Zhiqing-Xu/Filter_Life_Measurement/Design Draft/figs/5.jpg

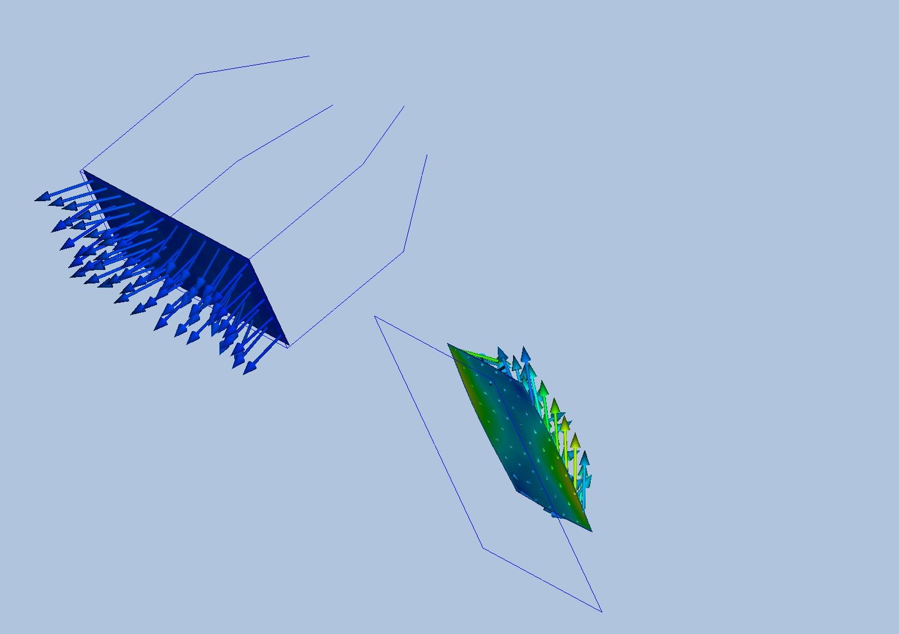
Design Draft/figs/5.jpg
