Zhiqing-Xu/Filter_Life_Measurement/Design Draft/Project01-APS490-CAD-CFD/CAD-Whole Sys Draft/blower/QUAT CAO AP.JPG

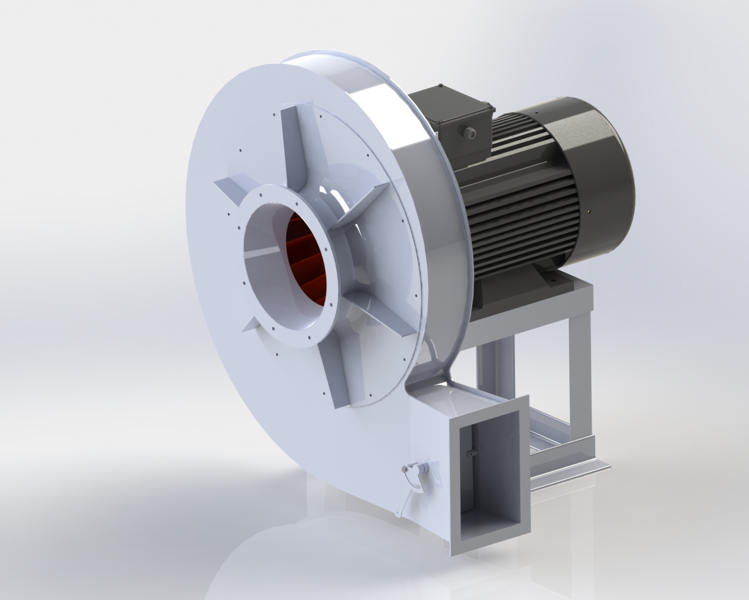
Design Draft/Project01-APS490-CAD-CFD/CAD-Whole Sys Draft/blower/QUAT CAO AP.JPG
