Zhiqing-Xu/Filter_Life_Measurement/Design Draft/Project01-APS490-CAD-CFD/CAD-Whole Sys Draft/butterfly valve/Sanitary-butterfly-valve-DIN11851-MxM-CAD-model-DN50-NO.jpg

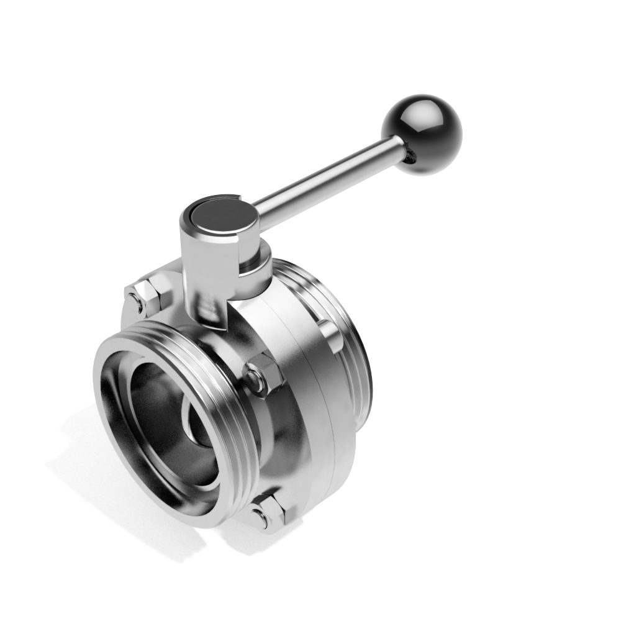
Design Draft/Project01-APS490-CAD-CFD/CAD-Whole Sys Draft/butterfly valve/Sanitary-butterfly-valve-DIN11851-MxM-CAD-model-DN50-NO.jpg
