Zhiqing-Xu/Filter_Life_Measurement/Design Draft/Project01-APS490-CAD-CFD/CAD-Whole Sys Final/other/Renderings/untitled.541.jpg

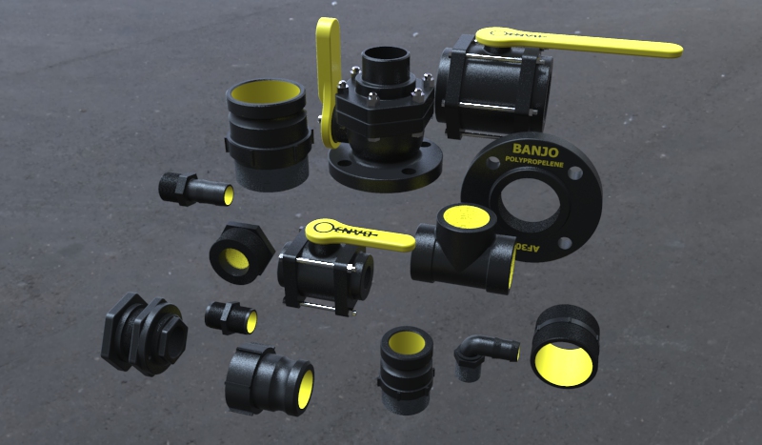
Design Draft/Project01-APS490-CAD-CFD/CAD-Whole Sys Final/other/Renderings/untitled.541.jpg
