Zhiqing-Xu/Filter_Life_Measurement/Design Draft/Project01-APS490-CAD-CFD/CFD/cfd_test_04/Design 1/Scenario 1/thumbnail.jpg

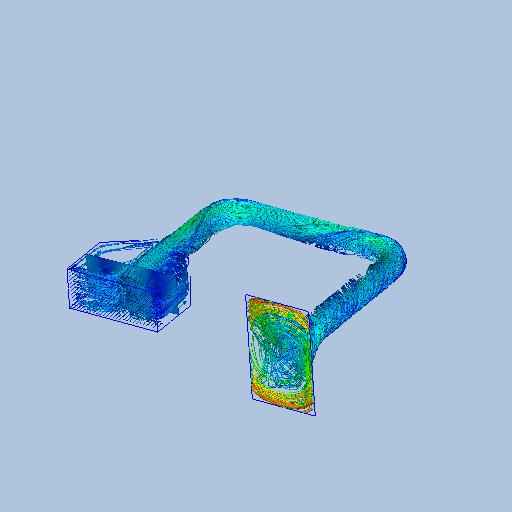
Design Draft/Project01-APS490-CAD-CFD/CFD/cfd_test_04/Design 1/Scenario 1/thumbnail.jpg
