Zhiqing-Xu/Filter_Life_Measurement/Final Design/FD_PNID.jpg

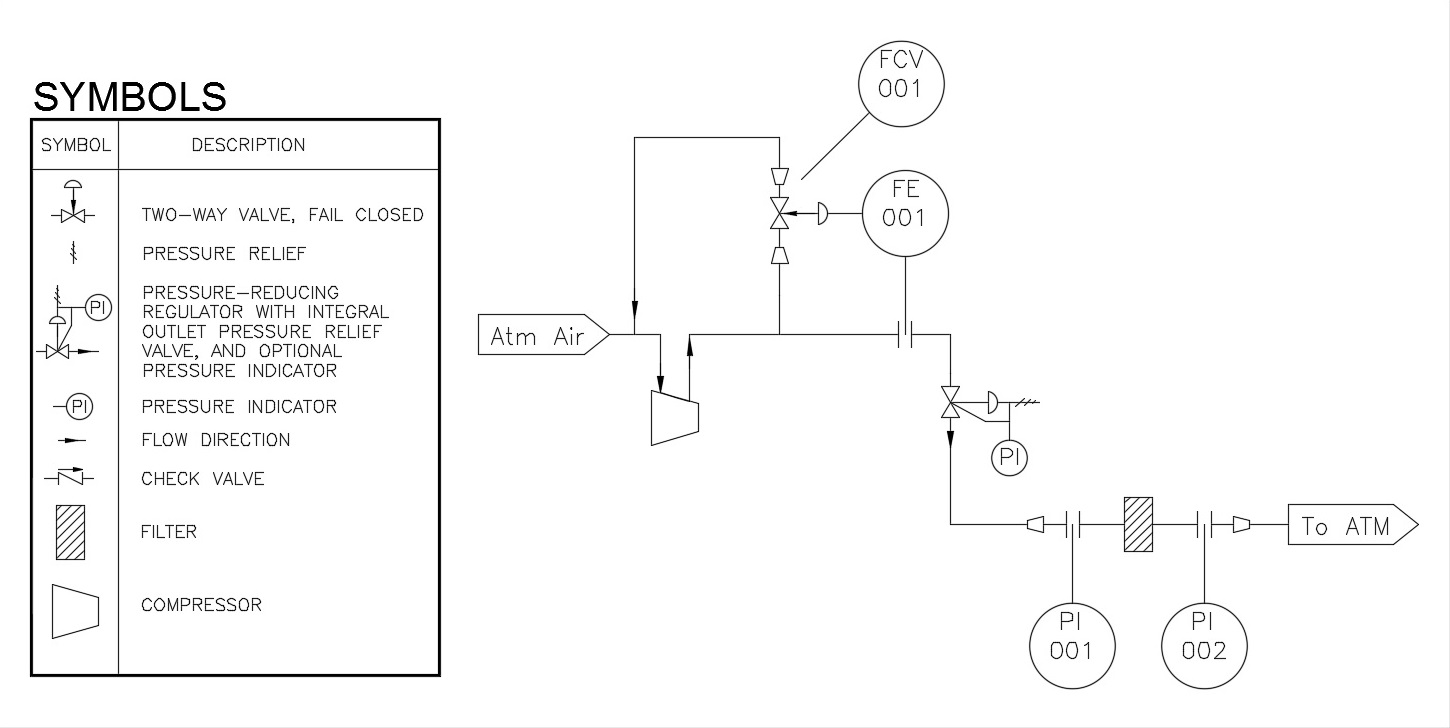
Final Design/FD_PNID.jpg
