Zhiqing-Xu/Filter_Life_Measurement/Final Design/Final Report Pik/1.png

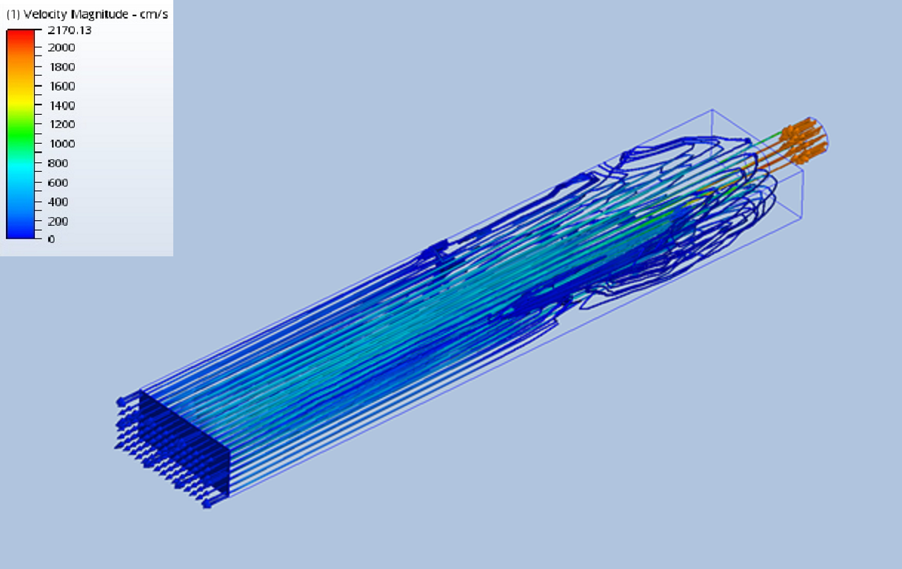
Final Design/Final Report Pik/1.png
