Zhiqing-Xu/Filter_Life_Measurement/Final Design/Project01-APS490-CAD-CFD2/CFD/cfd_test_04_support_1_support_2_support_support/Design 1/Scenario 1/thumbnail.jpg

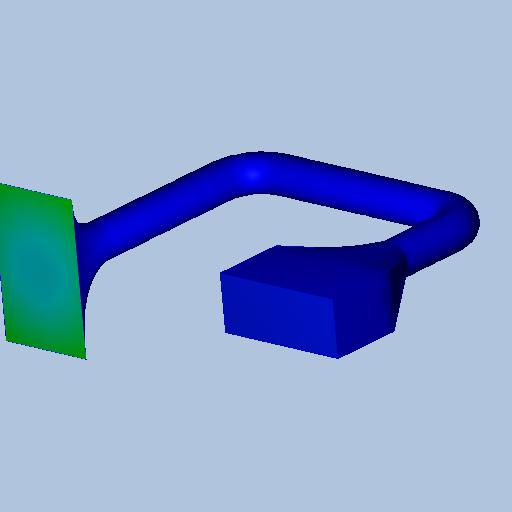
Final Design/Project01-APS490-CAD-CFD2/CFD/cfd_test_04_support_1_support_2_support_support/Design 1/Scenario 1/thumbnail.jpg
