Zhiqing-Xu/Filter_Life_Measurement/Final Design/TE_PNID.jpg

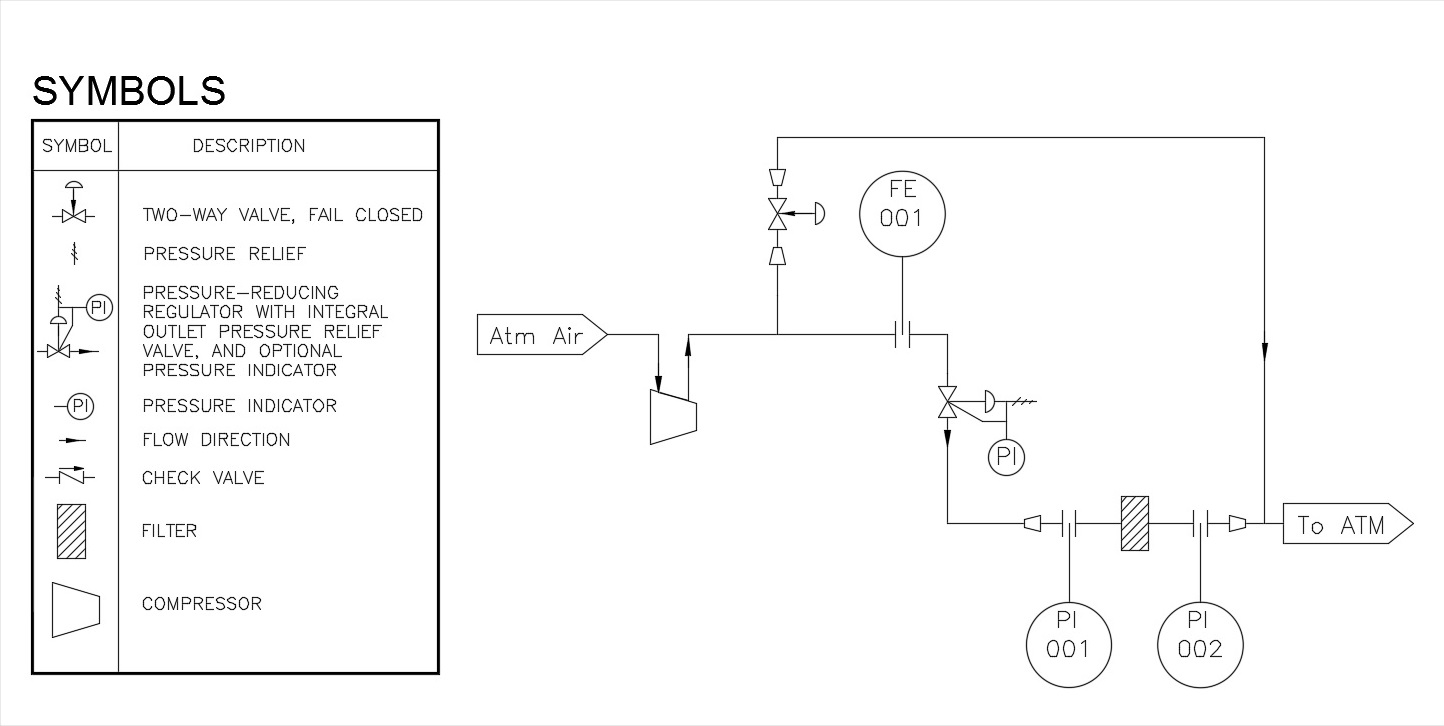
Final Design/TE_PNID.jpg
