Zhiqing-Xu/Filter_Life_Measurement/Final Design/Project01-APS490-CAD-CFD2/CAD-Whole Sys Final2/blower/MAT BICH.SLDASM

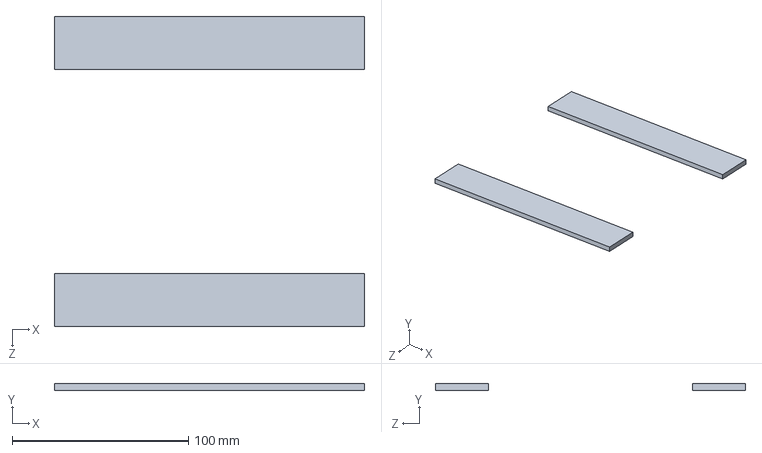
[picture p91: CAD file, 2023-04-30]
Final Design/Project01-APS490-CAD-CFD2/CAD-Whole Sys Final2/blower/MAT BICH.SLDASM
176.0 x 4.00 x 176.0 mm
LA x 2
