Zhiqing-Xu/Filter_Life_Measurement/Final Design/Project01-APS490-CAD-CFD2/CAD-Mahtab filters/filter 01/new.SLDASM

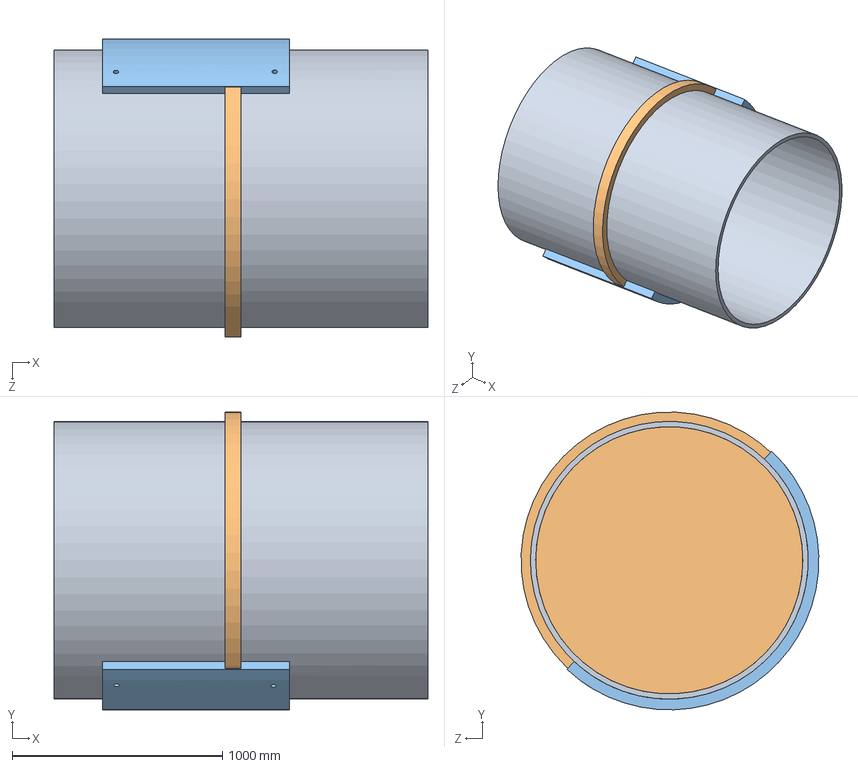
[picture p92: CAD file, 2023-04-30]
Final Design/Project01-APS490-CAD-CFD2/CAD-Mahtab filters/filter 01/new.SLDASM
1778.0 x 1414.8 x 1414.8 mm
safety valve filter
cavity
