Zhiqing-Xu/Filter_Life_Measurement/Design Draft/Project01-APS490-CAD-CFD/CAD-Mahtab filters/filter 02/a.SLDASM

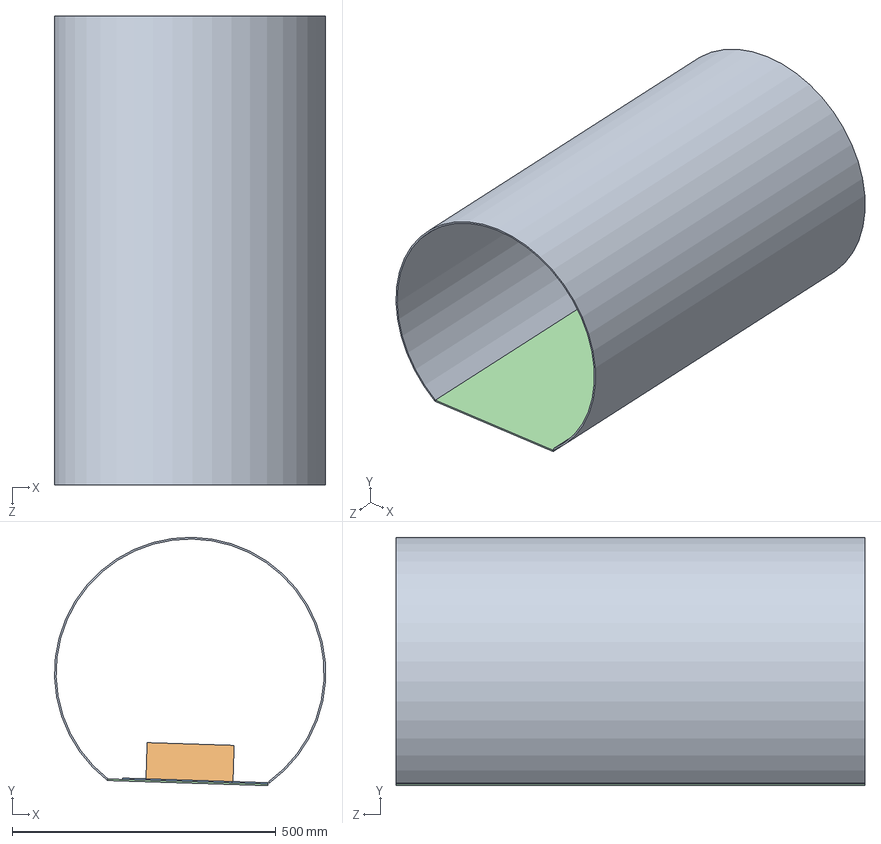
[picture p93: CAD file, 2023-04-30]
Design Draft/Project01-APS490-CAD-CFD/CAD-Mahtab filters/filter 02/a.SLDASM
513.7 x 470.7 x 889.0 mm
Part3sheet x 2
base
