Zhiqing-Xu/Filter_Life_Measurement/Design Draft/Project01-APS490-CAD-CFD/CAD-Whole Sys Draft/filter and gauge/filter/Assem3.SLDASM

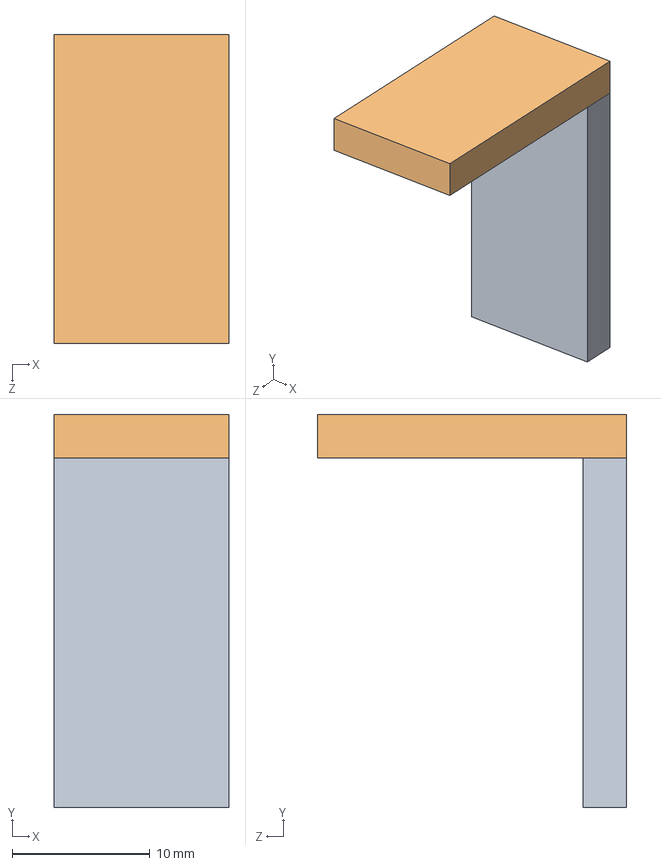
[picture p94: CAD file, 2023-04-30]
Design Draft/Project01-APS490-CAD-CFD/CAD-Whole Sys Draft/filter and gauge/filter/Assem3.SLDASM
12.7 x 28.6 x 22.5 mm
rec1
rec2
