Zhiqing-Xu/Filter_Life_Measurement/Final Design/Project01-APS490-CAD-CFD/CAD-Whole Sys Draft/blower/QUAT HUT.SLDASM

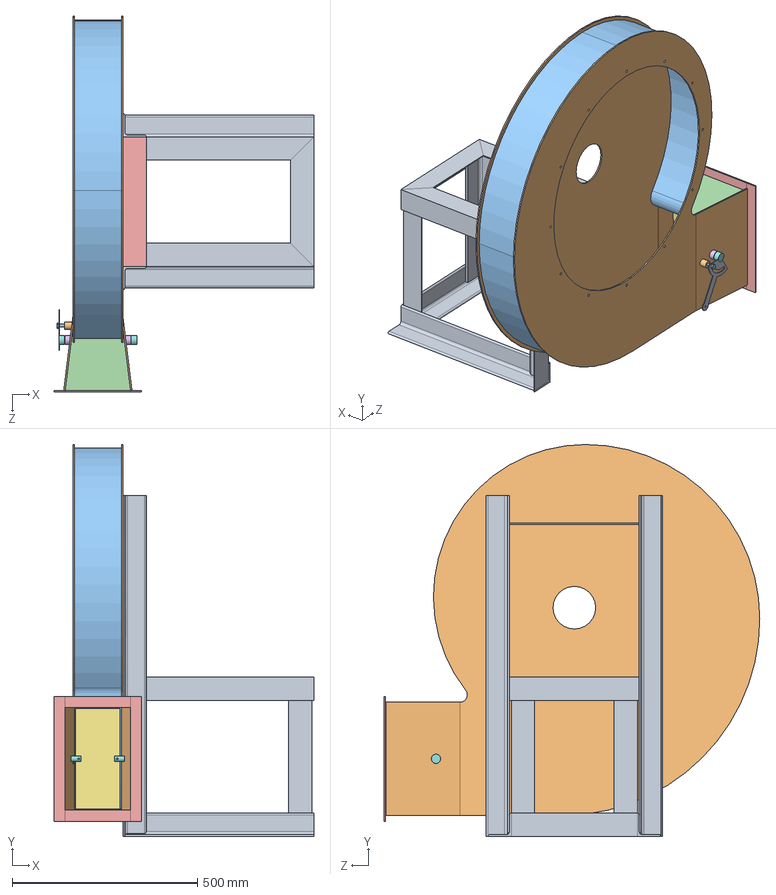
[picture p95: CAD file, 2023-04-30]
Final Design/Project01-APS490-CAD-CFD/CAD-Whole Sys Draft/blower/QUAT HUT.SLDASM
700.5 x 1057.0 x 1012.6 mm
KHUNG DO MAY
MAT TRUOC x 2
MAT HONG
MAT HONG 2 x 2
LA x 5
CHOT x 2
LA VAN GIO
BAT VAN x 2
TAY CAM KHOA GIO
CHOT 2
hex screw gradec_iso
