Zhiqing-Xu/Filter_Life_Measurement/Final Design/Project01-APS490-CAD-CFD2/CAD-Mahtab filters/filter 02/Mounted.SLDASM

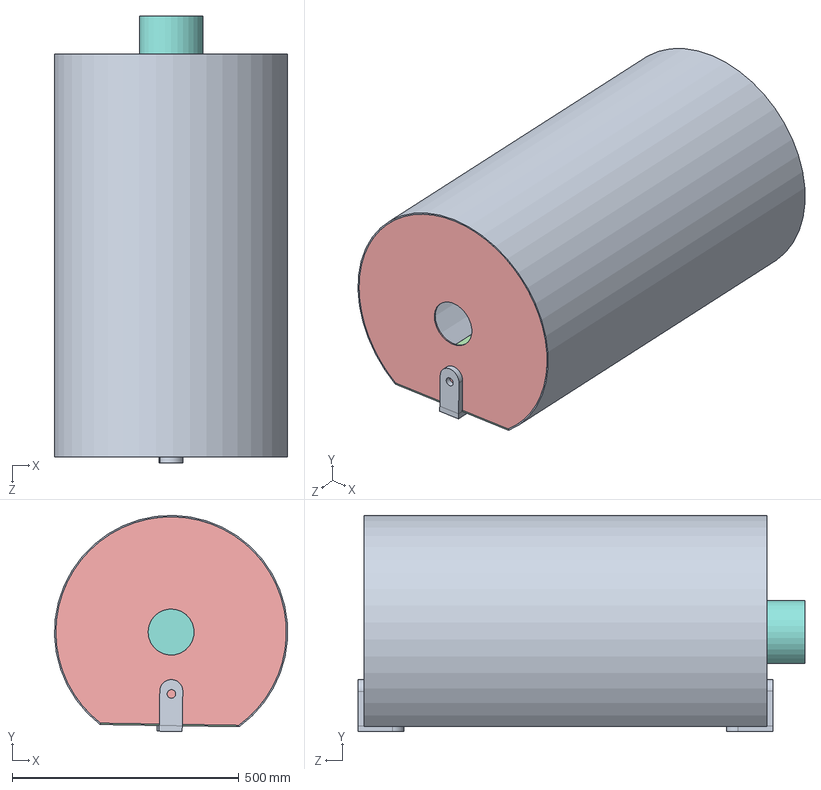
[picture p96: CAD file, 2023-04-30]
Final Design/Project01-APS490-CAD-CFD2/CAD-Mahtab filters/filter 02/Mounted.SLDASM
513.7 x 476.6 x 985.4 mm
Part3sheet x 2
base
cap1
Part1-cylind_filter
cap2
duct
