Zhiqing-Xu/Filter_Life_Measurement/Final Design/Project01-APS490-CAD-CFD2/CAD-Whole Sys Final/blower/DAU GIAM AP.SLDASM

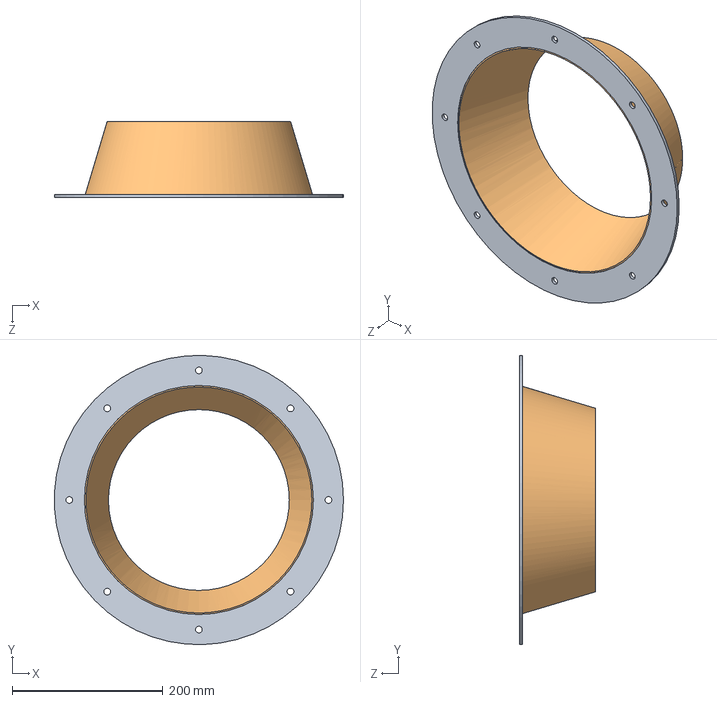
[picture p97: CAD file, 2023-04-30]
Final Design/Project01-APS490-CAD-CFD2/CAD-Whole Sys Final/blower/DAU GIAM AP.SLDASM
383.7 x 383.8 x 100.6 mm
MAT BICH
GIAM
