Zhiqing-Xu/Filter_Life_Measurement/Design Draft/Project01-APS490-CAD-CFD/CAD-Mahtab filters/filter 02/fixture.SLDASM

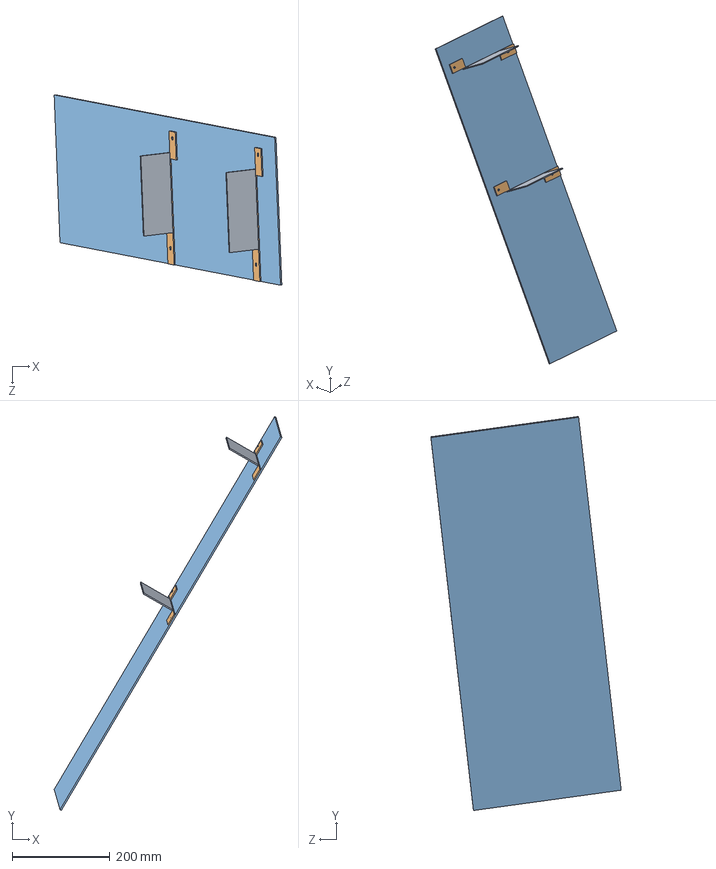
[picture p98: CAD file, 2023-04-30]
Design Draft/Project01-APS490-CAD-CFD/CAD-Mahtab filters/filter 02/fixture.SLDASM
465.0 x 804.6 x 389.0 mm
Part3sheet x 2
base
