Zhiqing-Xu/Filter_Life_Measurement/Design Draft/Project01-APS490-CAD-CFD/CAD-Whole Sys Final/blower/COT QUAT.SLDASM

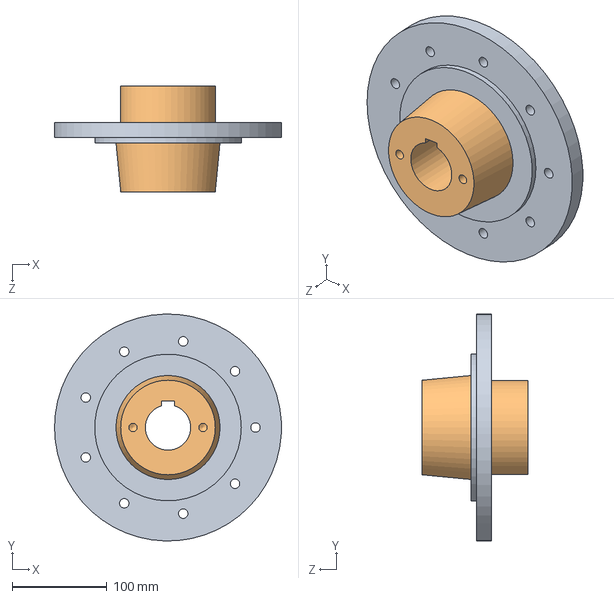
[picture p99: CAD file, 2023-04-30]
Design Draft/Project01-APS490-CAD-CFD/CAD-Whole Sys Final/blower/COT QUAT.SLDASM
240.0 x 239.9 x 112.0 mm
MAYO
COT CANH
