Zhiqing-Xu/Filter_Life_Measurement/Final Design/Project01-APS490-CAD-CFD2/CAD-Mahtab filters/filter 01/Assem3.SLDASM

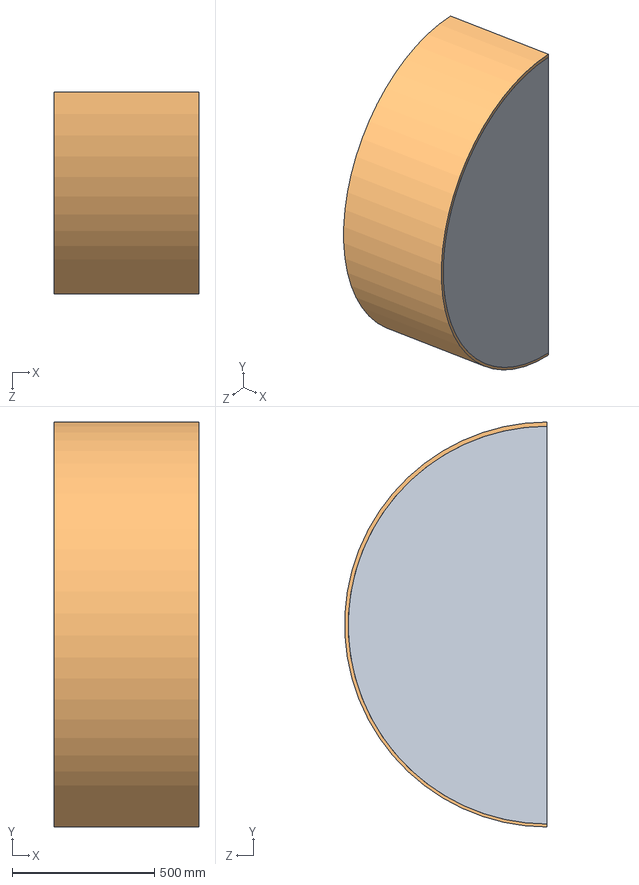
[picture p100: CAD file, 2023-04-30]
Final Design/Project01-APS490-CAD-CFD2/CAD-Mahtab filters/filter 01/Assem3.SLDASM
508.0 x 1422.4 x 710.2 mm
aas
aa
