Zhiqing-Xu/Filter_Life_Measurement/Final Design/Project01-APS490-CAD-CFD2/CAD-Mahtab filters/filter 02/fix2.SLDASM

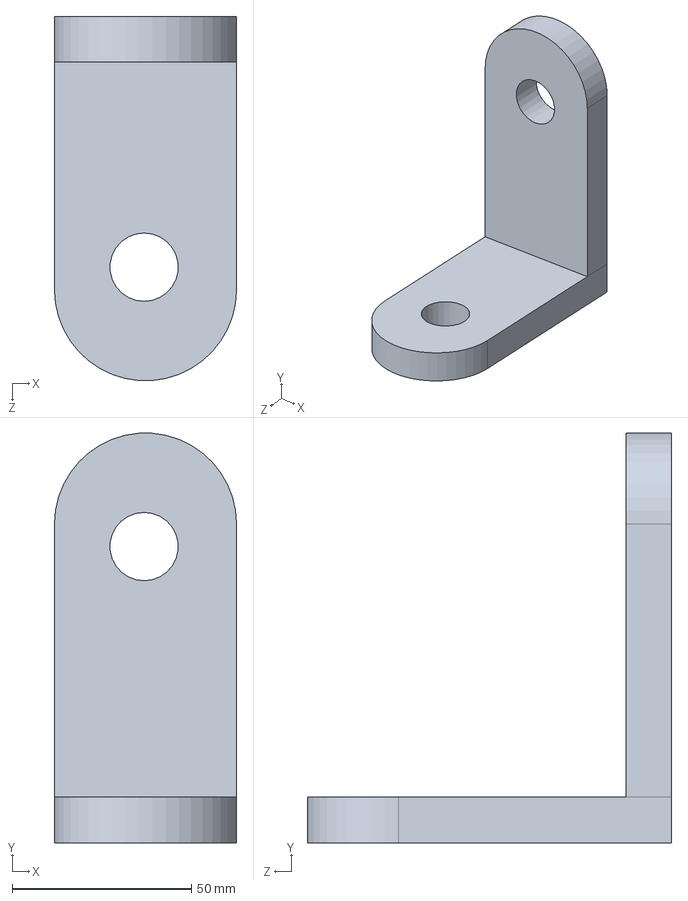
[picture p101: CAD file, 2023-04-30]
Final Design/Project01-APS490-CAD-CFD2/CAD-Mahtab filters/filter 02/fix2.SLDASM
50.8 x 114.2 x 101.5 mm
