Zhiqing-Xu/Filter_Life_Measurement/Design Draft/Project01-APS490-CAD-CFD/CAD-Mahtab filters/filter 02/Assem2.SLDASM

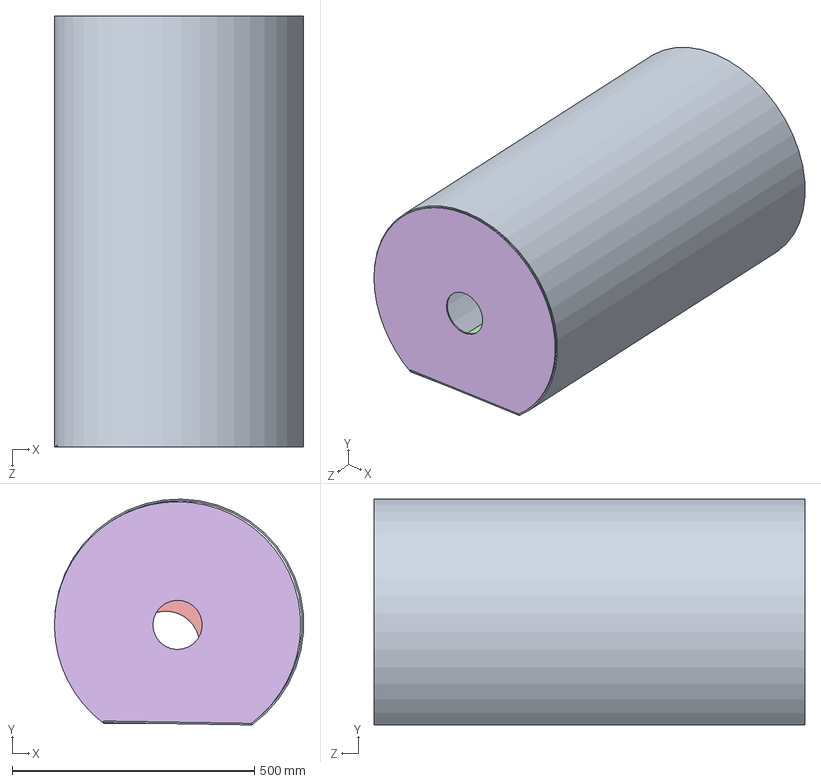
[picture p102: CAD file, 2023-04-30]
Design Draft/Project01-APS490-CAD-CFD/CAD-Mahtab filters/filter 02/Assem2.SLDASM
513.8 x 465.9 x 889.0 mm
Part3sheet x 2
base
Part1-cylind_filter
cap1
