Zhiqing-Xu/Filter_Life_Measurement/Final Design/Project01-APS490-CAD-CFD2/CAD-Mahtab filters/filter 01/Assem1.SLDASM

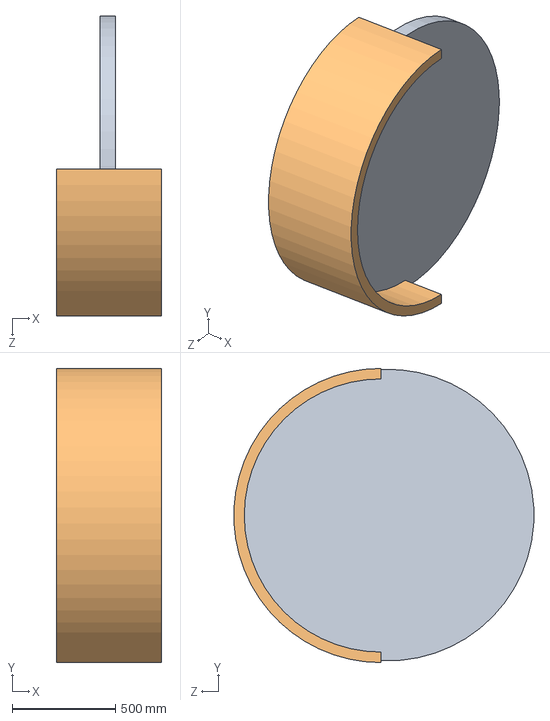
[picture p103: CAD file, 2023-04-30]
Final Design/Project01-APS490-CAD-CFD2/CAD-Mahtab filters/filter 01/Assem1.SLDASM
508.0 x 1422.4 x 1450.9 mm
skinwithcut
