Zhiqing-Xu/Filter_Life_Measurement/Design Draft/Project01-APS490-CAD-CFD/CAD-Mahtab filters/filter 01/final1.SLDASM

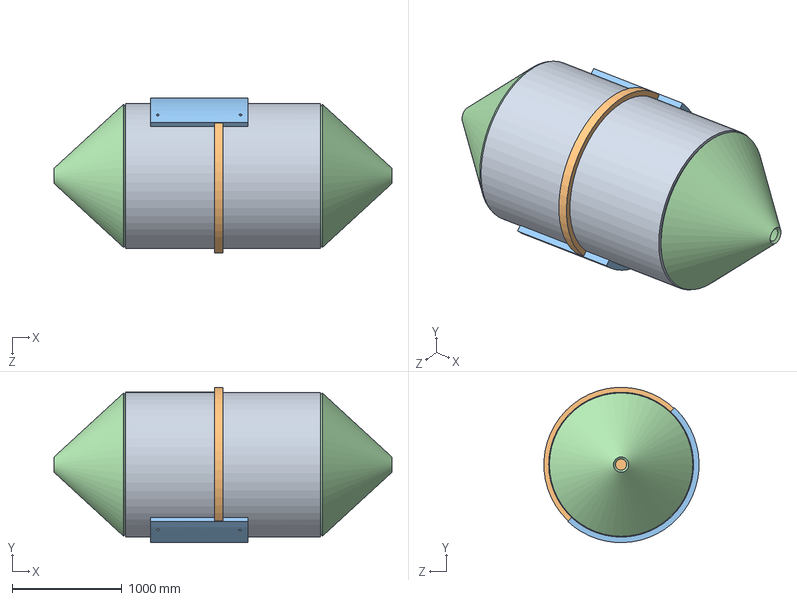
[picture p104: CAD file, 2023-04-30]
Design Draft/Project01-APS490-CAD-CFD/CAD-Mahtab filters/filter 01/final1.SLDASM
3082.4 x 1414.8 x 1414.8 mm
safety valve filter
cavity
