Zhiqing-Xu/Filter_Life_Measurement/Final Design/Project01-APS490-CAD-CFD2/CAD-Whole Sys Final2/filter prototype/Assem1.SLDASM

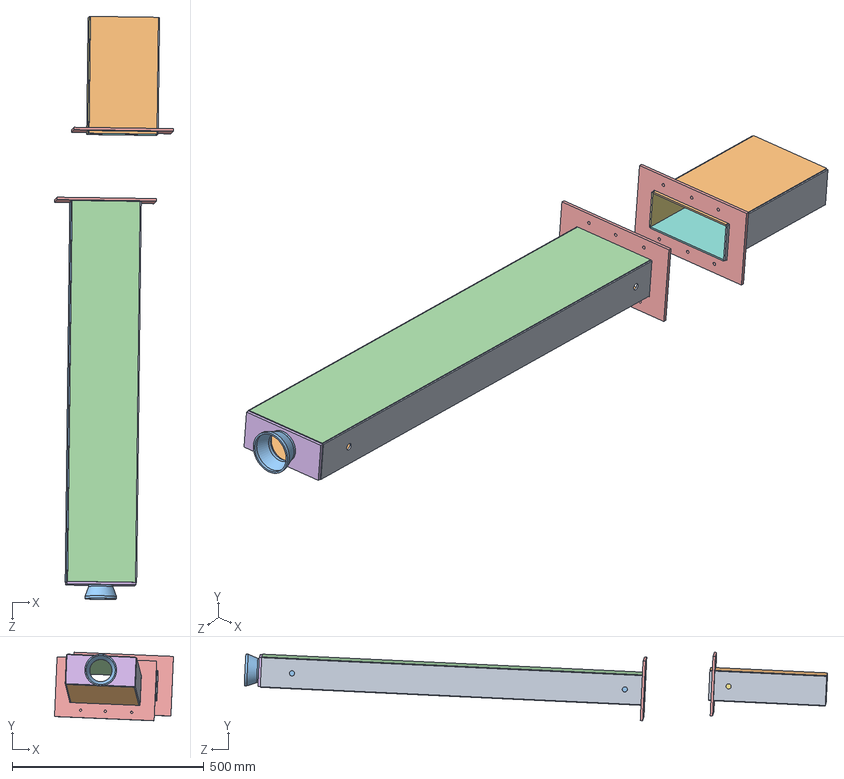
[picture p106: CAD file, 2023-04-30]
Final Design/Project01-APS490-CAD-CFD2/CAD-Whole Sys Final2/filter prototype/Assem1.SLDASM
310.1 x 178.7 x 1520.0 mm
sideWithHole
Bottom
side
top
sleevex2 x 2
inlet
side_1
Bottom_1
sideWithHole_1
top_1
PVC-fitting
