Zhiqing-Xu/Filter_Life_Measurement/Final Design/Project01-APS490-CAD-CFD2/CAD-Whole Sys Final2/filter prototype/Assem2.SLDASM

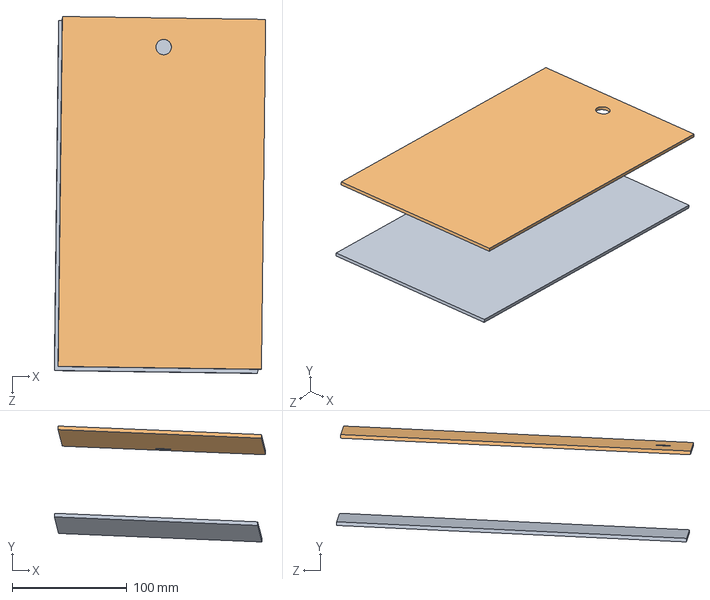
[picture p107: CAD file, 2023-04-30]
Final Design/Project01-APS490-CAD-CFD2/CAD-Whole Sys Final2/filter prototype/Assem2.SLDASM
183.9 x 100.9 x 310.6 mm
Bottom_1
top_1
