Zhiqing-Xu/Filter_Life_Measurement/Final Design/Project01-APS490-CAD-CFD2/CAD-Whole Sys Draft/blower/MAT TROI.SLDASM

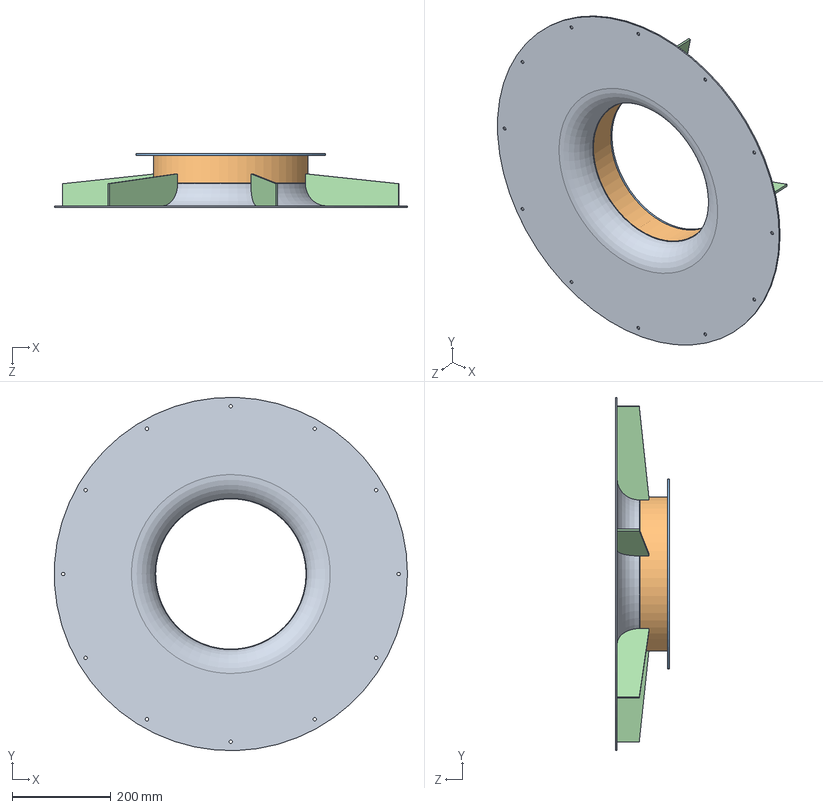
[picture p108: CAD file, 2023-04-30]
Final Design/Project01-APS490-CAD-CFD2/CAD-Whole Sys Draft/blower/MAT TROI.SLDASM
713.4 x 713.7 x 109.0 mm
TAM TRUOC
DOAN ONG
MAT BICH
BAT x 6
