Zhiqing-Xu/Filter_Life_Measurement/Design Draft/Project01-APS490-CAD-CFD/CAD-Mahtab filters/filter 01/aa.SLDPRT

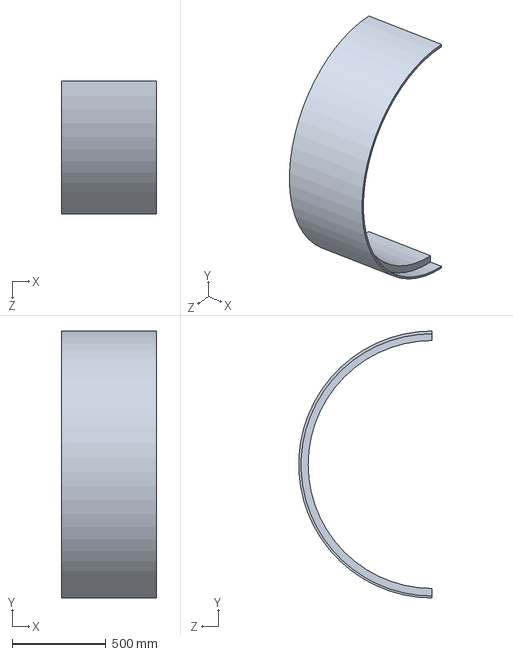
[picture p109: CAD file, 2023-04-30]
Design Draft/Project01-APS490-CAD-CFD/CAD-Mahtab filters/filter 01/aa.SLDPRT
508.0 x 1422.4 x 710.2 mm
