Zhiqing-Xu/Filter_Life_Measurement/Design Draft/Project01-APS490-CAD-CFD/CAD-Mahtab filters/filter 02/cap2.SLDPRT

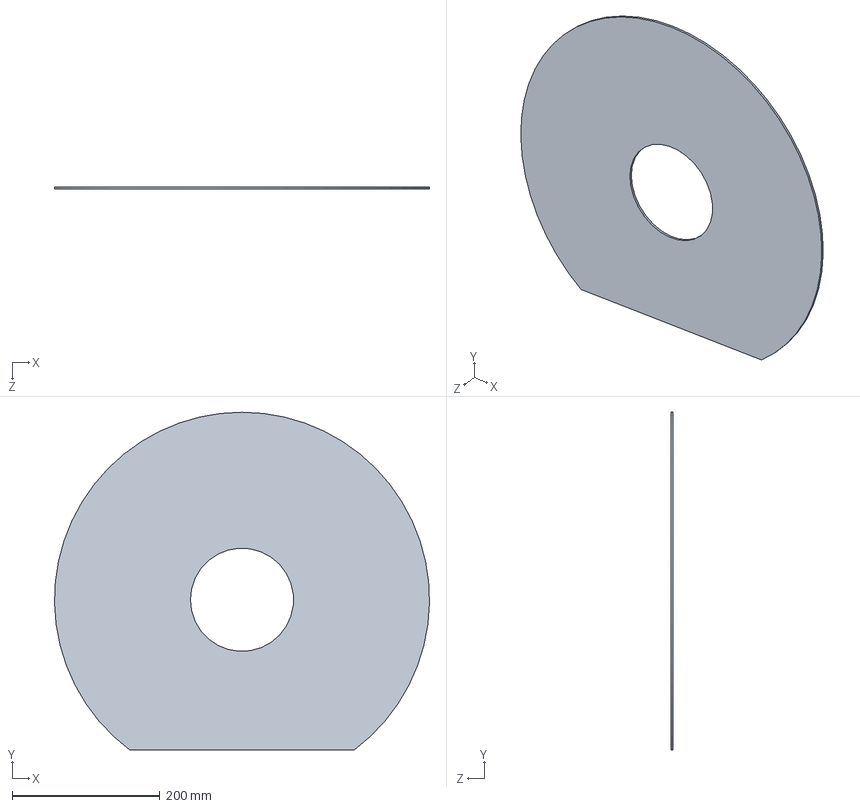
[picture p110: CAD file, 2023-04-30]
Design Draft/Project01-APS490-CAD-CFD/CAD-Mahtab filters/filter 02/cap2.SLDPRT
507.9 x 457.2 x 3.17 mm
