Zhiqing-Xu/Filter_Life_Measurement/Design Draft/Project01-APS490-CAD-CFD/CAD-Mahtab filters/filter 03/loftedpart.SLDPRT

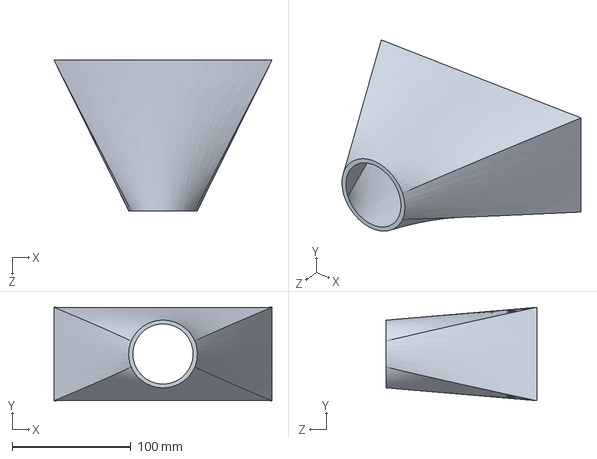
[picture p111: CAD file, 2023-04-30]
Design Draft/Project01-APS490-CAD-CFD/CAD-Mahtab filters/filter 03/loftedpart.SLDPRT
183.9 x 78.9 x 127.0 mm
