Zhiqing-Xu/Filter_Life_Measurement/Final Design/Project01-APS490-CAD-CFD2/CFD/test06_1_support_3/test06_1_support_3_1.docx

test06_1_support_3

Prepared by: User

Date: Friday, March 17, 2017

# Design 1

Length units | cm
Coordinate system | Cartesian 3D

## Scenario 1

### Materials

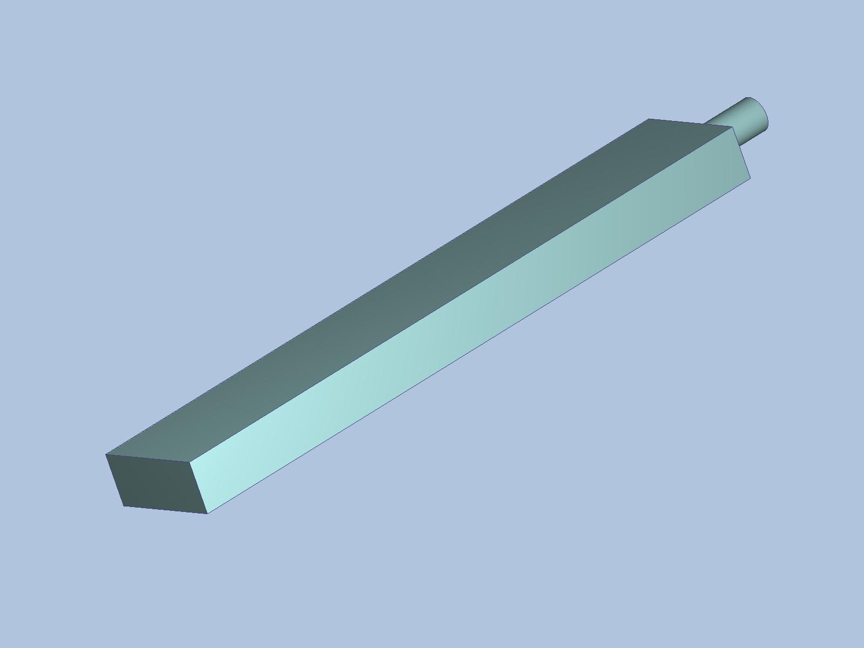
[picture p134: figure]

Name | ASSIGNED TO | PROPERTIES
Air | Part1.Solid1 | Density Equation of State Viscosity 1.817e-05 Pa-s Conductivity 0.02563 W/m-K Specific heat 1004.0 J/kg-K Compressibility 1.4 Emissivity 1.0 Wall roughness 0.0 meter Phase Vapor Pressure

### boundary conditions

Type | ASSIGNED TO
External Fan(1) | Surface:1
Mass Flow Rate(2.4 lbm/min) | Surface:2

### Initial Conditions

Type | ASSIGNED TO
Pressure(1.5 psi Gage) | Surface:1

### mesh

#### Automatic Meshing Settings

Surface refinement | 0
Gap refinement | 0
Resolution factor | 1.0
Edge growth rate | 1.1
Minimum points on edge | 2
Points on longest edge | 10
Surface limiting aspect ratio | 20

#### Mesh Enhancement Settings

Mesh enhancement | 1
Enhancement blending | 0
Number of layers | 3
Layer factor | 0.45
Layer gradation | 1.05

#### Meshed Model

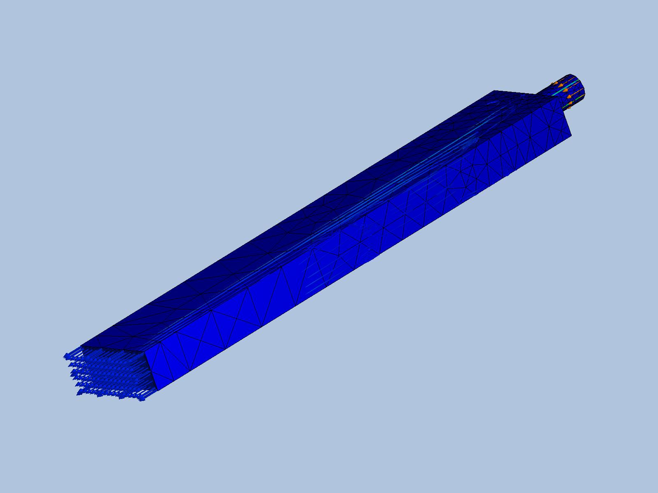
[picture p135: figure]

Number of Nodes | 2238
Number of Elements | 5753

### Physics

Flow | On
Compressibility | Subsonic
Heat Transfer | Off
Auto Forced Convection | Off
Gravity Components | 0.0, 0.0, 0.0
Radiation | Off
Scalar | No scalar
Turbulence | On

### Solver Settings

Solution mode | Steady State
Solver computer | MyComputer
Intelligent solution control | On
Advection scheme | ADV 5
Turbulence model | k-epsilon

### Convergence

Iterations run | 314
Solve time | 144 seconds
Solver version | 17.0.20160317

#### Energy Balance

#### Mass Balance

| In | Out
Mass flow | 41.5036 g/s | N.A.
Volume flow | 34450.4 cm^3/s | N.A.

### Results

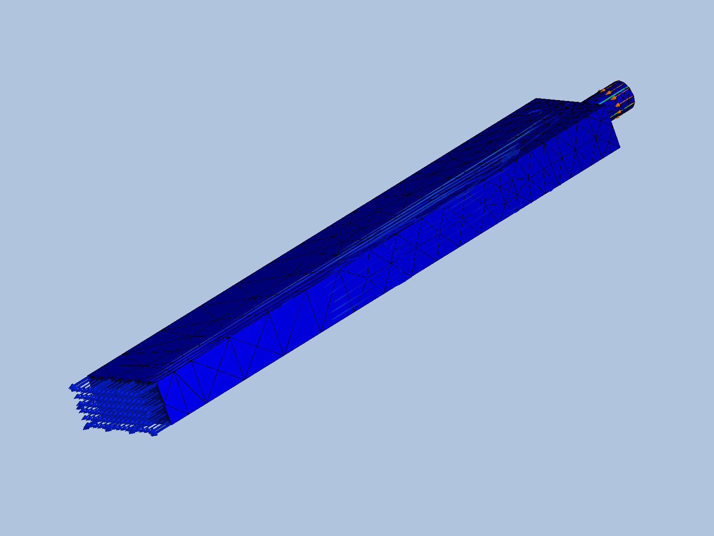
[picture p136: figure]

#### Inlets and Outlets

inlet 1 | inlet bulk pressure 1969.47 dyne/cm^2 inlet bulk temperature -0.0 C inlet mach number 0.00302521 mass flow in -18.16 g/s minimum x,y,z of opening 0.0 node near minimum x,y,z of opening 5.0 reynolds number 8586.53 surface id 2.0 volume flow in -15073.9 cm^3/s
inlet 2 | inlet bulk pressure 1969.48 dyne/cm^2 inlet bulk temperature 0.0 C inlet mach number 0.073169 mass flow in 59.6636 g/s minimum x,y,z of opening 0.0 node near minimum x,y,z of opening 18.0 reynolds number 74638.0 surface id 1.0 total mass flow in 41.5036 g/s total vol. flow in 34450.4 cm^3/s volume flow in 49524.3 cm^3/s

#### Field Variable Results

Variable | Max | Min
cond | 0.0002563 W/cm-K | 0.0002563 W/cm-K
dens | 0.00120473 g/cm^3 | 0.00120473 g/cm^3
econd | 0.298647 W/cm-K | 0.0002563 W/cm-K
emiss | 1.0 | 1.0
evisc | 0.378218 g/cm-s | 0.0001817 g/cm-s
gent | 11925.9 1/s | 1.528 1/s
press | 1969.48 dyne/cm^2 | 1969.47 dyne/cm^2
ptotl | 7888.18 dyne/cm^2 | 1969.47 dyne/cm^2
scal1 | 0.0 | 0.0
seebeck | 0.0 V/K | 0.0 V/K
shgc | 0.0 | 0.0
spech | 1.004 J/g-K | 1.004 J/g-K
temp | 0.0 C | 0.0 C
transmiss | 0.0 | 0.0
turbd | 44005000.0 cm^2/s^3 | 2.99895e-06 cm^2/s^3
turbk | 244494.0 cm^2/s^2 | 1.817e-07 cm^2/s^2
ufactor | 0.0 | 0.0
visc | 0.0001817 g/cm-s | 0.0001817 g/cm-s
vx vel | 383.402 cm/s | -148.946 cm/s
vy vel | 235.64 cm/s | -281.253 cm/s
vz vel | 640.446 cm/s | -3134.6 cm/s
wrough | 0.0 cm | 0.0 cm

#### Component Thermal Summary

Part | Minimum Temperature | Maximum Temperature | Volume Averaged Temperature
Part1.Solid1 | 0 | 0 | 0

#### Fluid Forces on Walls

pressx | 0.00017451 dynes
pressy | -0.0051892 dynes
pressz | 228710.0 dynes
shearx | 17.539 dynes
sheary | -1.028 dynes
shearz | -8878.3 dynes

# Decision Center

Page 1 Generated with Autodesk CFD 2017

test06_1_support_3.cfdst Prepared by: User
