Zhiqing-Xu/Filter_Life_Measurement/Design Draft/Project01-APS490-CAD-CFD/CFD/cfd_test_04_support_1_support/preview.jpg

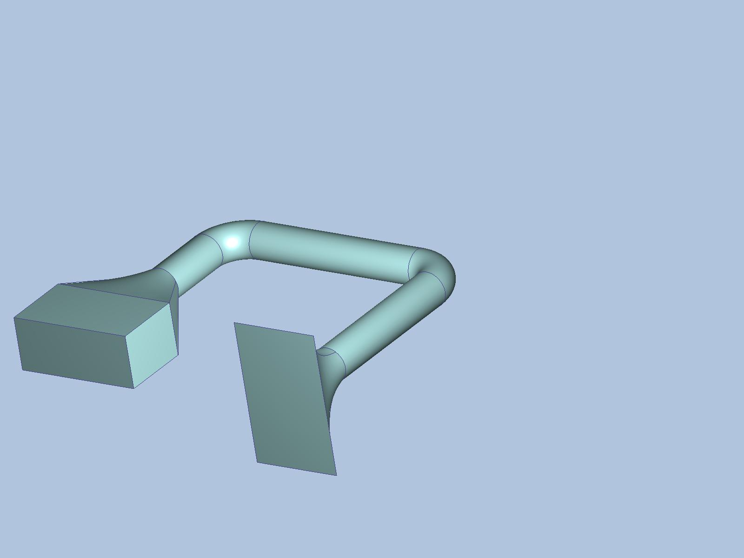
Design Draft/Project01-APS490-CAD-CFD/CFD/cfd_test_04_support_1_support/preview.jpg
