Zhiqing-Xu/Filter_Life_Measurement/Final Design/Project01-APS490-CAD-CFD2/CFD/test06_1_support/preview.jpg

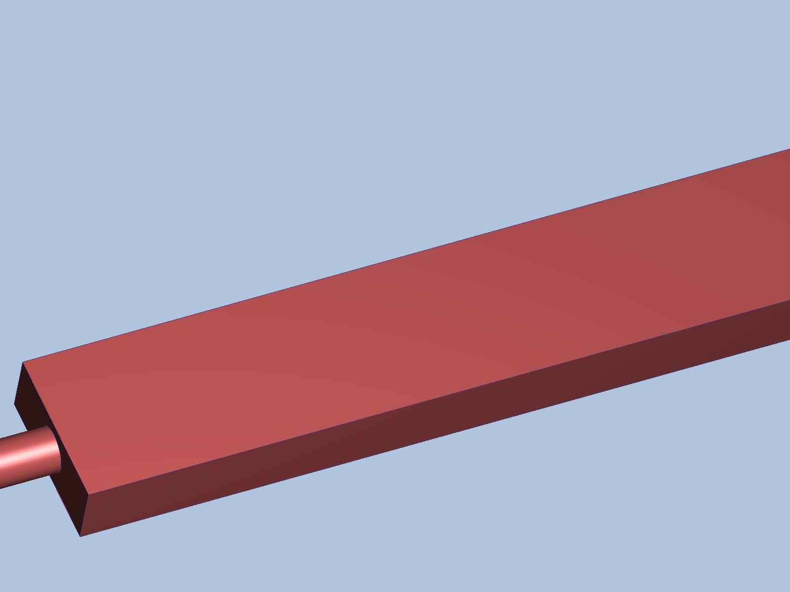
Final Design/Project01-APS490-CAD-CFD2/CFD/test06_1_support/preview.jpg
